wbledzinski/PV_PWM_HEATERv2/Mech/Screenshot 2021-02-02 153431.png

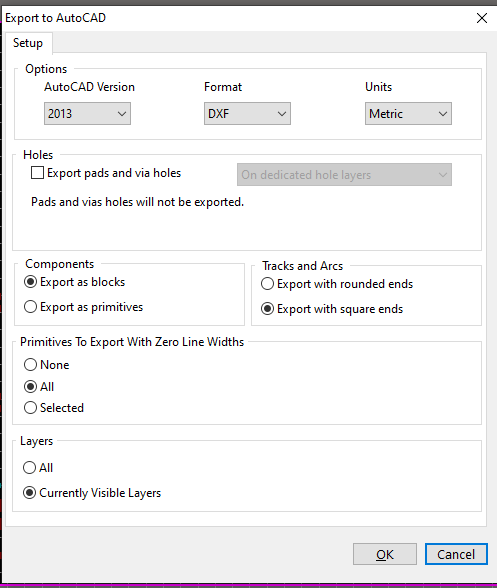
Mech/Screenshot 2021-02-02 153431.png
